treatbam/sw3518-rp2350-zero/src/sw3518.cpp

#include "sw3518.h"
#include <math.h>

namespace {
constexpr uint8_t REG_FCX_STATUS = 0x06;
constexpr uint8_t REG_I2C_CTRL = 0x13;
constexpr uint8_t REG_ADC_VIN_H = 0x30;
constexpr uint8_t REG_ADC_VIN_VOUT_L = 0x32;
constexpr uint8_t REG_ADC_TYPE = 0x3A;
constexpr uint8_t REG_ADC_H = 0x3B;
constexpr uint8_t REG_ADC_L = 0x3C;

constexpr uint8_t ADC_VIN = 1;
constexpr uint8_t ADC_VOUT = 2;
// Datasheet labels vs this board: user observed A/C swapped at types 3/4.
constexpr uint8_t ADC_IOUT_A = 4;
constexpr uint8_t ADC_IOUT_C = 3;

constexpr uint8_t I2C_CTRL_VIN_ADC_EN = 0x02;
constexpr uint16_t kWireTimeoutMs = 50;
}  // namespace

void SW3518::startBus(int sda, int scl, uint32_t hz) {
#if defined(WOKWI_SIM) && WOKWI_SIM
  (void)sda;
  (void)scl;
  (void)hz;
  busStarted_ = true;
  return;
#endif
#if defined(ESP32) || defined(ARDUINO_ARCH_ESP32)
  wire_.begin(sda, scl, hz);
  wire_.setTimeOut(kWireTimeoutMs);
#else
  wire_.setSDA(sda);
  wire_.setSCL(scl);
  wire_.begin();
  if (hz) wire_.setClock(hz);
#if defined(ARDUINO_ARCH_RP2040) || defined(ARDUINO_ARCH_RP2350)
  wire_.setTimeout(kWireTimeoutMs);
#endif
#endif
  busStarted_ = true;
}

bool SW3518::begin(int sda, int scl, uint32_t hz) {
#if defined(WOKWI_SIM) && WOKWI_SIM
  (void)sda;
  (void)scl;
  (void)hz;
  present_ = true;
  busStarted_ = true;
  return true;
#else
  startBus(sda, scl, hz);
  delay(20);
  if (probe()) rearm();
  return present_;
#endif
}

bool SW3518::probe() {
#if defined(WOKWI_SIM) && WOKWI_SIM
  present_ = true;
  return true;
#else
  if (!busStarted_) return false;
  wire_.beginTransmission(kAddr);
  present_ = (wire_.endTransmission() == 0);
  return present_;
#endif
}

bool SW3518::rearm() {
  if (!present_) return false;
#if defined(WOKWI_SIM) && WOKWI_SIM
  return true;
#else
  const bool ok = enableVinAdc();
  delay(5);
  return ok;
#endif
}

bool SW3518::writeReg(uint8_t reg, uint8_t val) {
  wire_.beginTransmission(kAddr);
  wire_.write(reg);
  wire_.write(val);
  return wire_.endTransmission() == 0;
}

bool SW3518::readReg(uint8_t reg, uint8_t& val) {
  wire_.beginTransmission(kAddr);
  wire_.write(reg);
  if (wire_.endTransmission(false) != 0) return false;
  if (wire_.requestFrom(static_cast<int>(kAddr), 1) != 1) return false;
  val = wire_.read();
  return true;
}

bool SW3518::enableVinAdc() {
  // Absolute write matches happyme531 / VFDclock; RMW can leave enable clear
  // if a prior read failed. Bit0 is one-shot PDO rebroadcast — leave it 0.
  return writeReg(REG_I2C_CTRL, I2C_CTRL_VIN_ADC_EN);
}

bool SW3518::readAdc(uint8_t type, uint16_t& raw) {
  if (!writeReg(REG_ADC_TYPE, type)) return false;
  delay(2);
  uint8_t hi = 0, lo = 0;
  if (!readReg(REG_ADC_H, hi)) return false;
  if (!readReg(REG_ADC_L, lo)) return false;
  raw = sw3518PackAdc(hi, lo);
  return true;
}

bool SW3518::readVinMv(uint16_t& out) {
  uint8_t vin_h = 0, vin_vout_l = 0;
  if (readReg(REG_ADC_VIN_H, vin_h) && readReg(REG_ADC_VIN_VOUT_L, vin_vout_l)) {
    const uint16_t raw = sw3518PackVinCont(vin_h, vin_vout_l);
    if (raw != 0) {
      out = sw3518VinMv(raw);
      return true;
    }
  }

  uint16_t raw = 0;
  if (!readAdc(ADC_VIN, raw)) return false;
  out = sw3518VinMv(raw);
  return true;
}

bool SW3518::readVoutMv(uint16_t& out) {
  uint16_t raw = 0;
  if (!readAdc(ADC_VOUT, raw)) return false;
  out = sw3518VoutMv(raw);
  return true;
}

bool SW3518::readIoutAMa(uint16_t& out) {
  uint16_t raw = 0;
  if (!readAdc(ADC_IOUT_A, raw)) return false;
  out = sw3518IoutMa(raw);
  return true;
}

bool SW3518::readIoutCMa(uint16_t& out) {
  uint16_t raw = 0;
  if (!readAdc(ADC_IOUT_C, raw)) return false;
  out = sw3518IoutMa(raw);
  return true;
}

bool SW3518::readProtocol(Protocol& out, uint8_t& pd_ver) {
  uint8_t st = 0;
  if (!readReg(REG_FCX_STATUS, st)) return false;
  pd_ver = (st >> 4) & 0x03;
  const uint8_t ind = st & 0x0F;
  if (ind <= 0x0B) out = static_cast<Protocol>(ind);
  else out = Protocol::Unknown;
  return true;
}

const char* SW3518::protocolName(Protocol p) {
  switch (p) {
    case Protocol::None: return "5V/DCP";
    case Protocol::QC2: return "QC2.0";
    case Protocol::QC3: return "QC3.0";
    case Protocol::FCP: return "FCP";
    case Protocol::SCP: return "SCP";
    case Protocol::PdFix: return "PD FIX";
    case Protocol::PdPps: return "PD PPS";
    case Protocol::PE11: return "PE1.1";
    case Protocol::PE20: return "PE2.0";
    case Protocol::LVDC: return "LVDC";
    case Protocol::SFCP: return "SFCP";
    case Protocol::AFC: return "AFC";
    default: return "?";
  }
}

bool SW3518::readSnapshot(Snapshot& s) {
#if defined(WOKWI_SIM) && WOKWI_SIM
  const uint32_t t = millis();
  const float wave = 0.5f + 0.5f * sinf(t / 900.0f);
  s.vin_mv = 12000;
  s.vout_mv = 9000;
  s.ic_ma = (uint16_t)(800 + 600 * wave);
  s.ia_ma = (uint16_t)(200 + 150 * (1.0f - wave));
  s.protocol = Protocol::PdFix;
  s.pd_ver = 2;
  s.power_a_w = (s.vout_mv / 1000.0f) * (s.ia_ma / 1000.0f);
  s.power_c_w = (s.vout_mv / 1000.0f) * (s.ic_ma / 1000.0f);
  s.power_total_w = s.power_a_w + s.power_c_w;
  s.ok = true;
  return true;
#else
  s = Snapshot{};
  if (!present_) return false;
  if (!readVinMv(s.vin_mv)) return false;
  if (!readVoutMv(s.vout_mv)) return false;
  if (!readIoutAMa(s.ia_ma)) return false;
  if (!readIoutCMa(s.ic_ma)) return false;
  if (!readProtocol(s.protocol, s.pd_ver)) return false;
  s.power_a_w = (s.vout_mv / 1000.0f) * (s.ia_ma / 1000.0f);
  s.power_c_w = (s.vout_mv / 1000.0f) * (s.ic_ma / 1000.0f);
  s.power_total_w = s.power_a_w + s.power_c_w;
  s.ok = true;
  return true;
#endif
}
